mattywausb/ElBanquos_kitchentimer/blender/Final Picutures/mk2.jpg

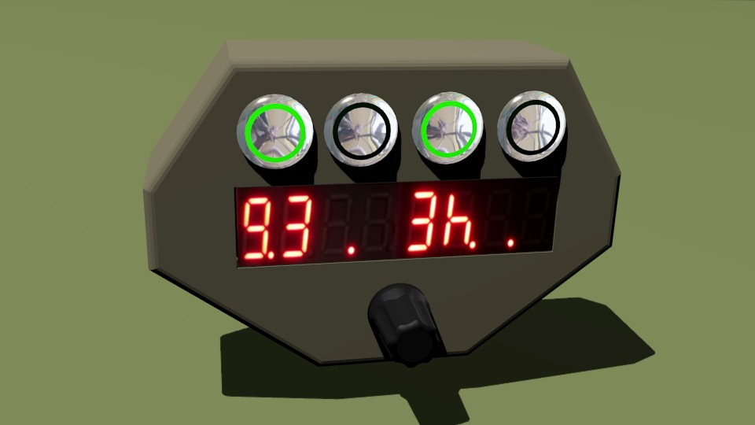
blender/Final Picutures/mk2.jpg
