mattywausb/ElBanquos_kitchentimer/blender/LED_Texture.JPG

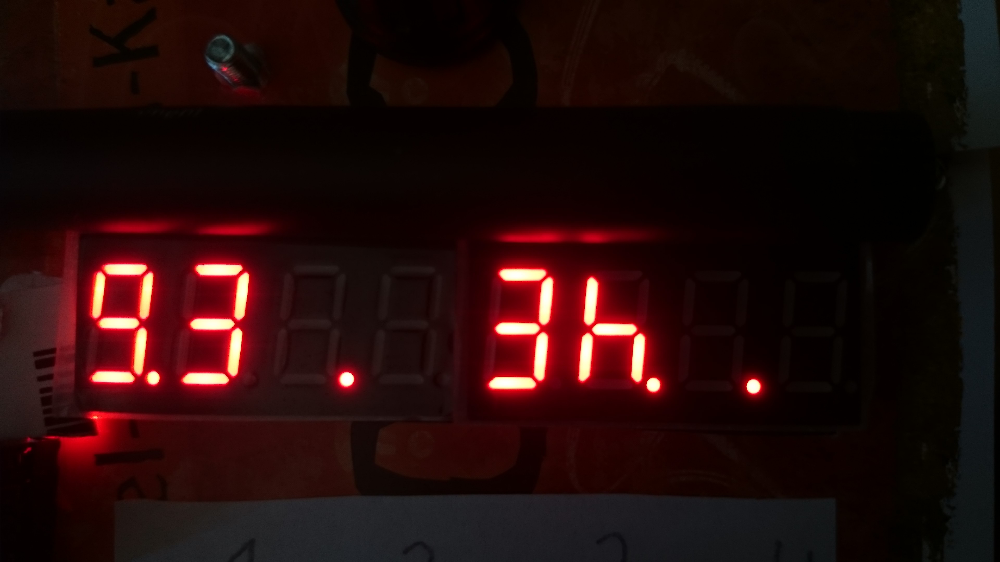
blender/LED_Texture.JPG
