mattywausb/ElBanquos_kitchentimer/blender/Reflection Backplate.jpg

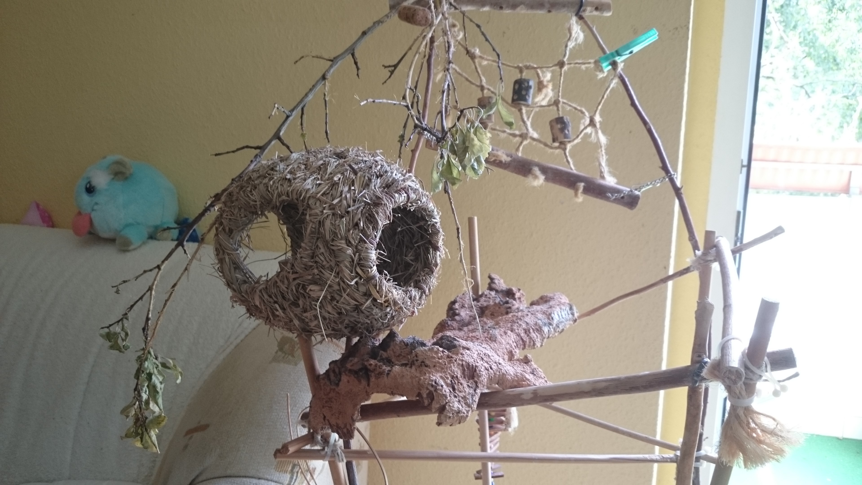
blender/Reflection Backplate.jpg
