mattywausb/ElBanquos_kitchentimer/fritzing/ElbanquosKitchentimer_MK2_Leiterplatte.png

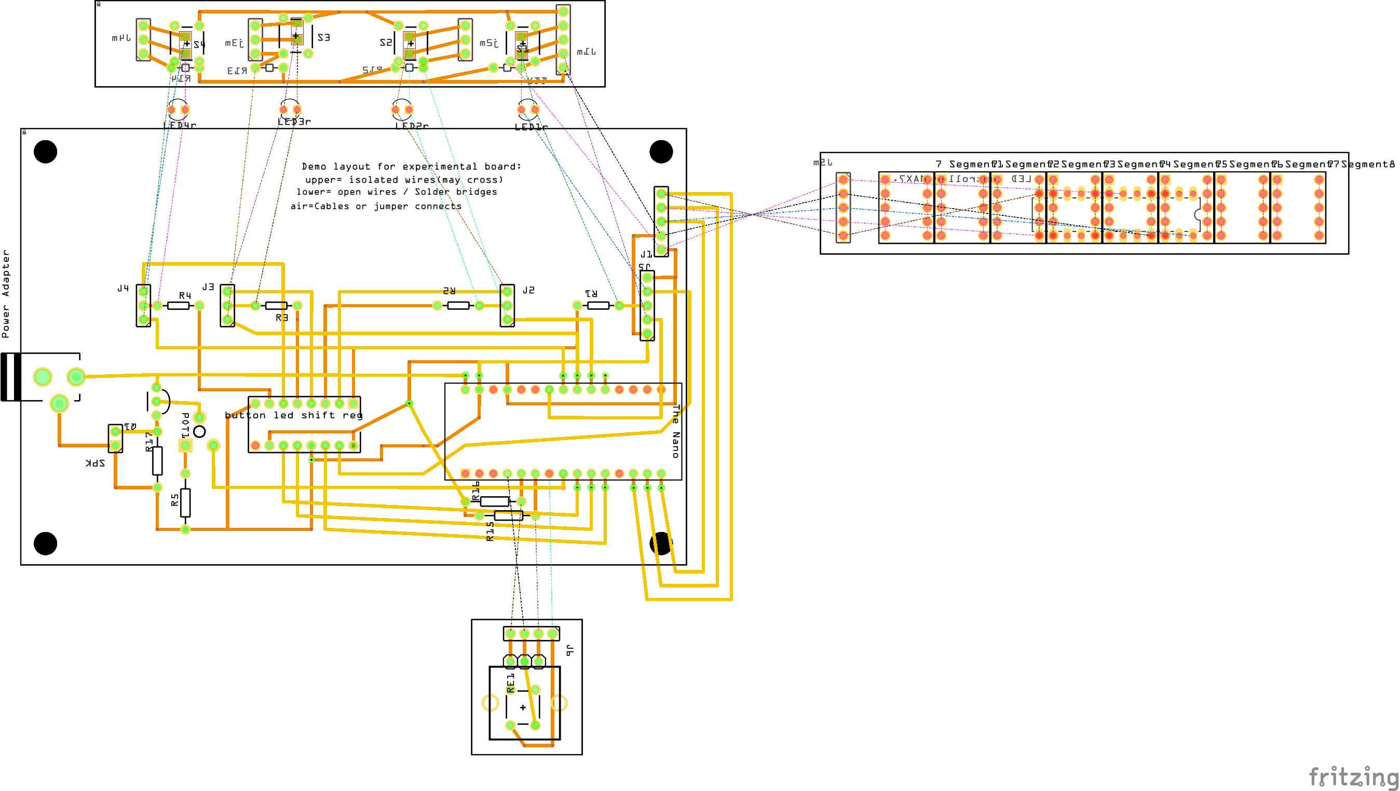
fritzing/ElbanquosKitchentimer_MK2_Leiterplatte.png
