mattywausb/ElBanquos_kitchentimer/fritzing/ElbanquosKitchentimer_MK2_Schaltplan.png

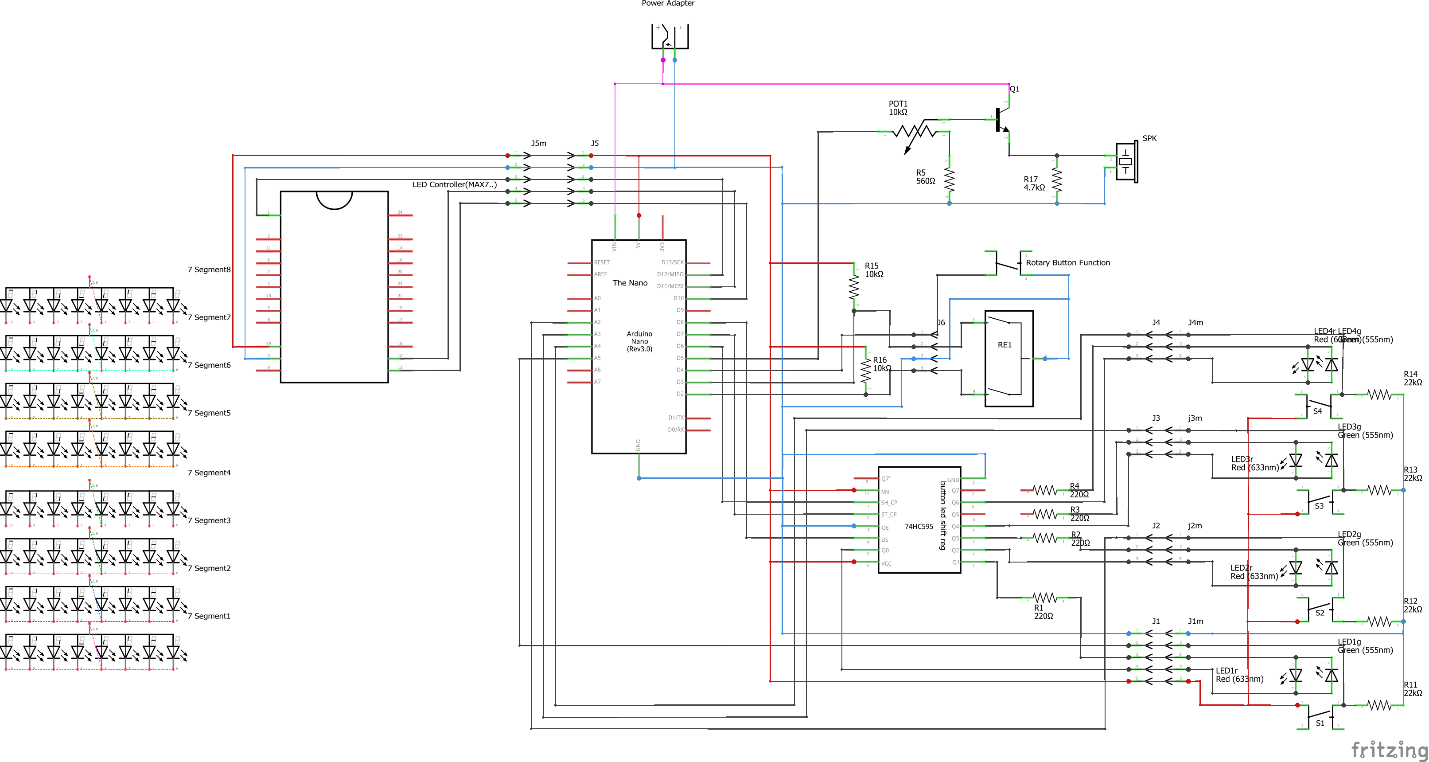
fritzing/ElbanquosKitchentimer_MK2_Schaltplan.png
