mattywausb/ElBanquos_kitchentimer/docs/build_pictures/03_prototype_on_breadboard.jpg

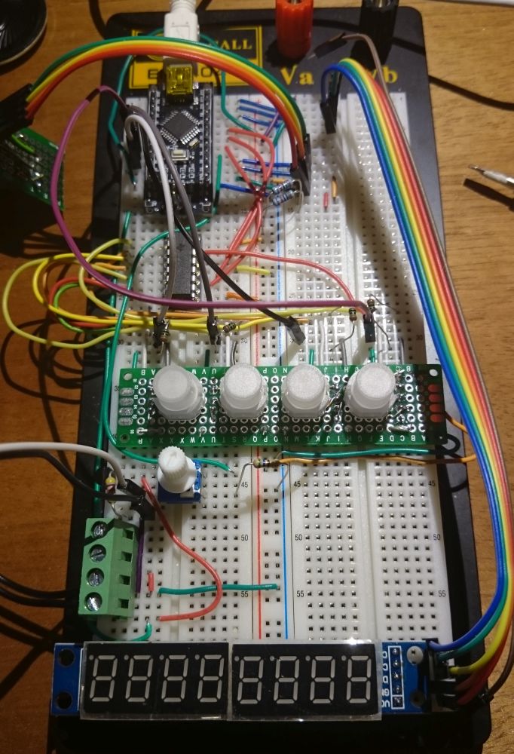
docs/build_pictures/03_prototype_on_breadboard.jpg
