mattywausb/ElBanquos_kitchentimer/docs/build_pictures/05_pcb_back.jpg

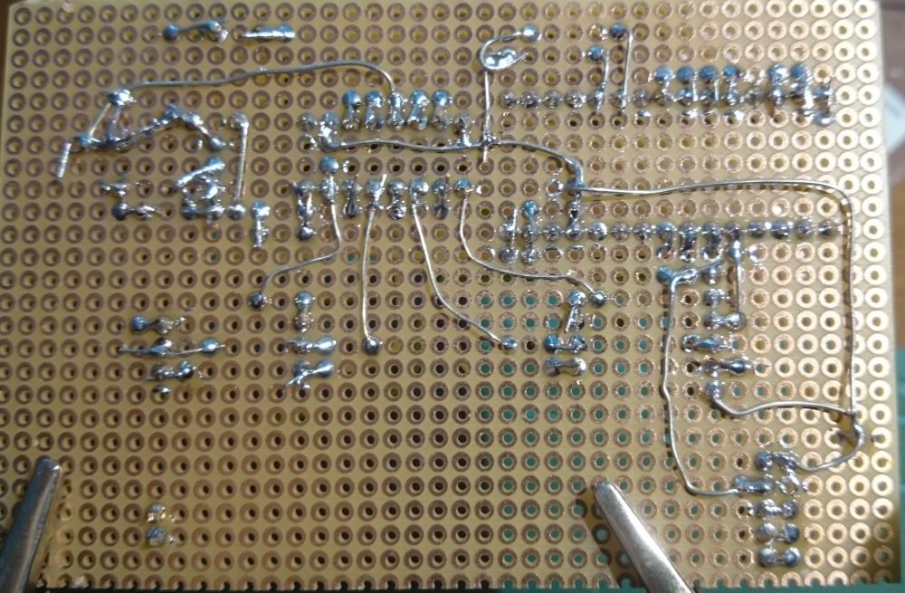
docs/build_pictures/05_pcb_back.jpg
