mattywausb/ElBanquos_kitchentimer/Arduino/tone-workbench2/mainSettings.h

#define TRACE_ON 

#define TIMER_COUNT 4
#define INDEX_FOR_UNDEFINED_TIMER 255

/* Global constants*/
#define NO_TIME_SELECTION -1

#define LEDRG_OFF   0x00
#define LEDRG_GREEN 0x02
#define LEDRG_RED   0x01
#define LEDRG_MASK  0x03
